colinleroy/adbusb/map.cpp

#include <Arduino.h>

uint8_t aek_to_hid(uint8_t adb_code) {
	switch(adb_code) {
		case 0x35: return 0x29;
		case 0x7A: return 0x3A;
		case 0x78: return 0x3B;
		case 0x63: return 0x3C;
		case 0x76: return 0x3D;
		case 0x60: return 0x3E;
		case 0x61: return 0x3F;
		case 0x62: return 0x40;
		case 0x64: return 0x41;
		case 0x65: return 0x42;
		case 0x6D: return 0x43;
		case 0x67: return 0x44;
		case 0x6F: return 0x45;
		case 0x69: return 0x46;
		case 0x6B: return 0x47;
		case 0x71: return 0x48;
		case 0x7F: return 0x66;

		case 0x32: return 0x35;
		case 0x12: return 0x1E;
		case 0x13: return 0x1F;
		case 0x14: return 0x20;
		case 0x15: return 0x21;
		case 0x17: return 0x22;
		case 0x16: return 0x23;
		case 0x1A: return 0x24;
		case 0x1C: return 0x25;
		case 0x19: return 0x26;
		case 0x1D: return 0x27;
		case 0x1B: return 0x2D;
		case 0x18: return 0x2E;
		case 0x33: return 0x2A;
		case 0x72: return 0x49;
		case 0x73: return 0x4A;
		case 0x74: return 0x4B;
		case 0x47: return 0x53;
		case 0x51: return 0x67;
		case 0x4B: return 0x54;
		case 0x43: return 0x55;

		case 0x30: return 0x2B;
		case 0x0C: return 0x14;
		case 0x0D: return 0x1A;
		case 0x0E: return 0x08;
		case 0x0F: return 0x15;
		case 0x11: return 0x17;
		case 0x10: return 0x1C;
		case 0x20: return 0x18;
		case 0x22: return 0x0C;
		case 0x1F: return 0x12;
		case 0x23: return 0x13;
		case 0x21: return 0x2F;
		case 0x1E: return 0x30;
		case 0x2A: return 0x32;
		case 0x75: return 0x4C;
		case 0x77: return 0x4D;
		case 0x79: return 0x4E;
		case 0x59: return 0x5F;
		case 0x5B: return 0x60;
		case 0x5C: return 0x61;
		case 0x4E: return 0x56;

		case 0x39: return 0x39;
		case 0x00: return 0x04;
		case 0x01: return 0x16;
		case 0x02: return 0x07;
		case 0x03: return 0x09;
		case 0x05: return 0x0A;
		case 0x04: return 0x0B;
		case 0x26: return 0x0D;
		case 0x28: return 0x0E;
		case 0x25: return 0x0F;
		case 0x29: return 0x33;
		case 0x27: return 0x34;
		case 0x24: return 0x28;
		case 0x56: return 0x5C;
		case 0x57: return 0x5D;
		case 0x58: return 0x5E;
		case 0x45: return 0x57;

		case 0x38: return 0xE1;
		case 0x0A: return 0x64; // iso only
		case 0x06: return 0x1D;
		case 0x07: return 0x1B;
		case 0x08: return 0x06;
		case 0x09: return 0x19;
		case 0x0B: return 0x05;
		case 0x2D: return 0x11;
		case 0x2E: return 0x10;
		case 0x2B: return 0x36;
		case 0x2F: return 0x37;
		case 0x2C: return 0x38;
		case 0x7B: return 0xE5;
		case 0x3E: return 0x52;
		case 0x53: return 0x59;
		case 0x54: return 0x5A;
		case 0x55: return 0x5B;

		case 0x36: return 0xE0;
		case 0x3A: return 0xE2;
		case 0x37: return 0xE3;
		case 0x31: return 0x2C;
		case 0x7C: return 0xE6;
		case 0x7D: return 0xE4;
		case 0x3B: return 0x50;
		case 0x3D: return 0x51;
		case 0x3C: return 0x4F;
		case 0x52: return 0x62;
		case 0x41: return 0x63;
		case 0x4C: return 0x58;

		default: return false;
	}
}

uint8_t modifier_to_bitmask(uint8_t hid_code) {
    switch(hid_code) {
		case 0xE0: return (1<<0);  // left ctrl
        case 0xE1: return (1<<1);  // left shift
        case 0xE2: return (1<<2);  // left opt
        case 0xE3: return (1<<3);  // left cmd
        case 0xE4: return (1<<4);  // right ctrl
        case 0xE5: return (1<<5);  // right shift
        case 0xE6: return (1<<6);  // right opt
		default: return false;
    }
}
